mikew123/dic_ws/3dPrinted/Dicotomy-SwichProtectorClips.3mf

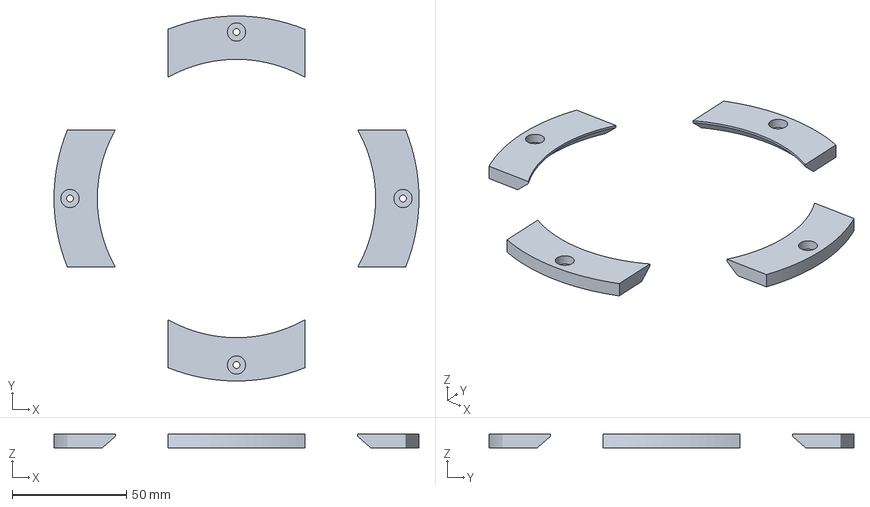
[picture p24: CAD file, 2026-02-28]
3dPrinted/Dicotomy-SwichProtectorClips.3mf
160.0 x 160.0 x 6.00 mm
