mikew123/dic_ws/3dPrinted/Dicotomy-clip.3mf

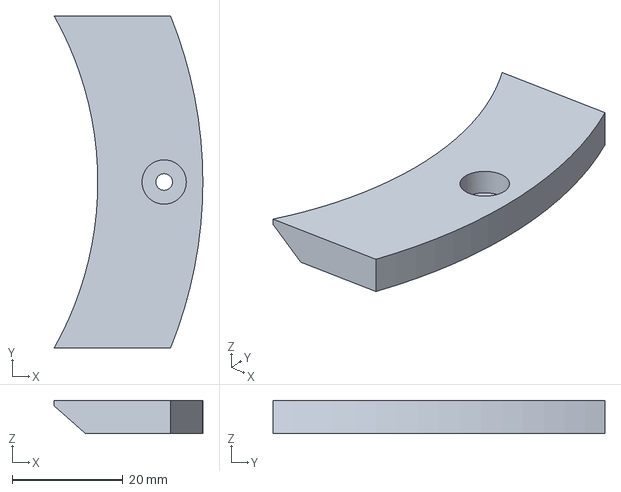
[picture p25: CAD file, 2026-02-28]
3dPrinted/Dicotomy-clip.3mf
26.9 x 60.0 x 6.00 mm
