mikew123/dic_ws/3dPrinted/Dicotomy-ElecMount.3mf

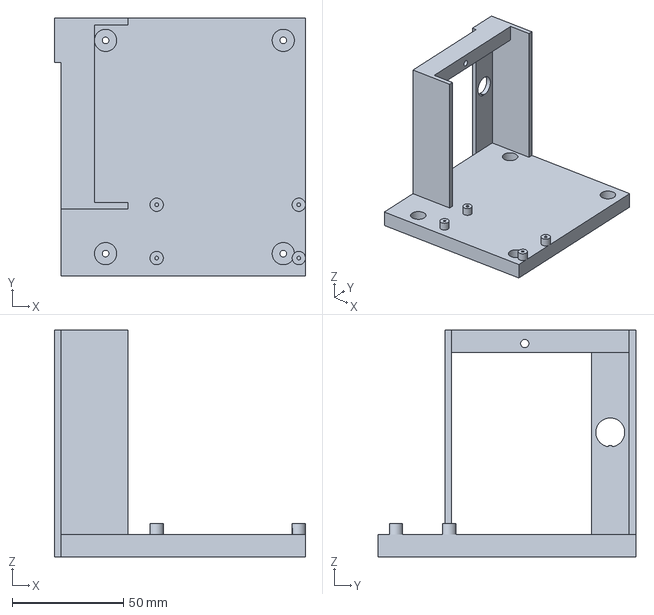
[picture p26: CAD file, 2026-02-23]
3dPrinted/Dicotomy-ElecMount.3mf
113.0 x 116.0 x 102.0 mm
