mikew123/dic_ws/3dPrinted/Dicotomy-CenteringRing.3mf

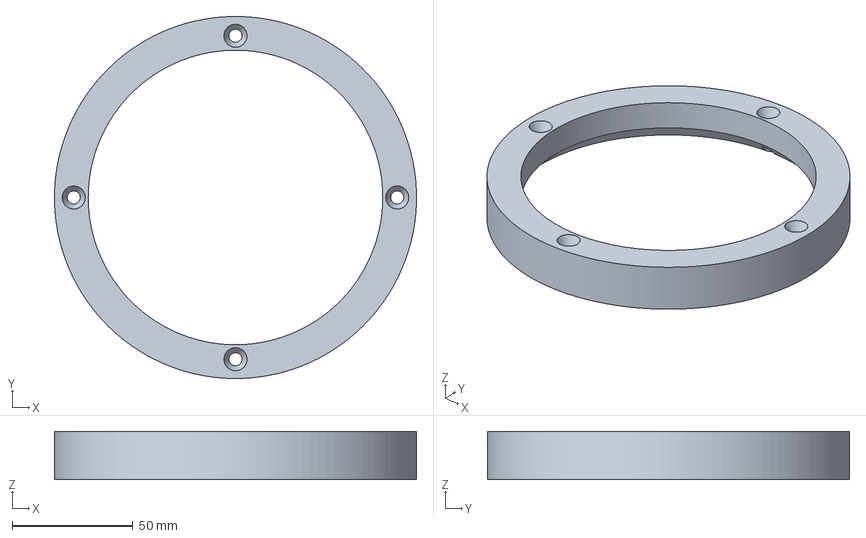
[picture p27: CAD file, 2026-02-21]
3dPrinted/Dicotomy-CenteringRing.3mf
150.0 x 150.0 x 20.0 mm
