mikew123/dic_ws/3dPrinted/Dicotomy-CenterHousing.3mf

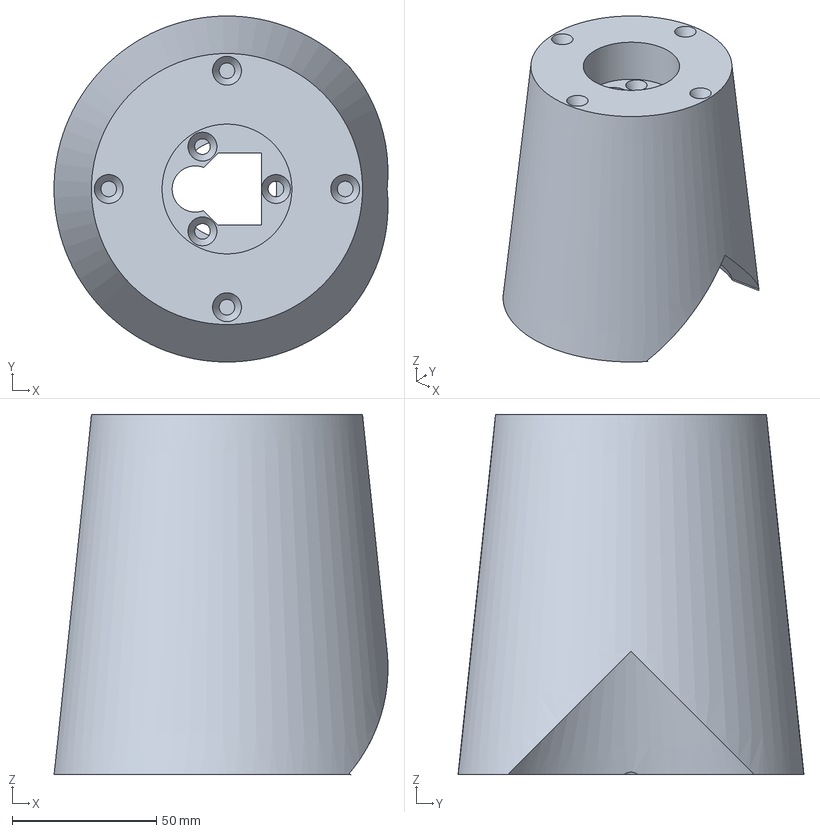
[picture p28: CAD file, 2026-02-21]
3dPrinted/Dicotomy-CenterHousing.3mf
115.8 x 120.0 x 125.0 mm
