mikew123/dic_ws/3dPrinted/Dicotomy-HumpCurved.3mf

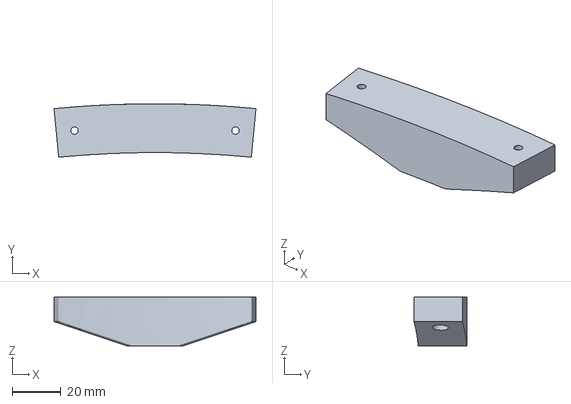
[picture p29: CAD file, 2026-02-21]
3dPrinted/Dicotomy-HumpCurved.3mf
82.8 x 21.9 x 20.0 mm
