mikew123/dic_ws/3dPrinted/Dicotomy-LimitSwHump.3mf

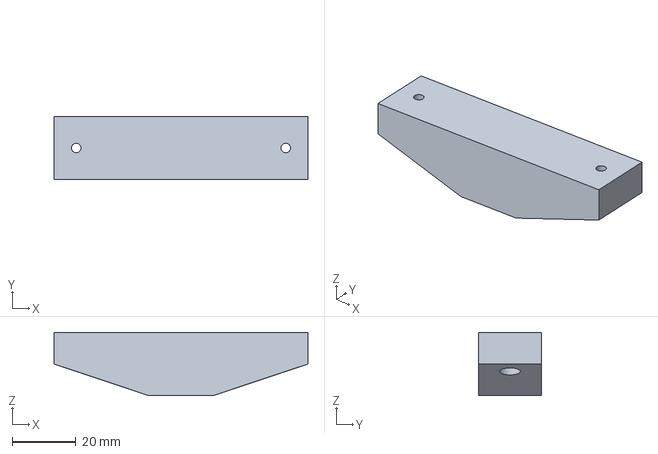
[picture p30: CAD file, 2026-02-21]
3dPrinted/Dicotomy-LimitSwHump.3mf
80.0 x 20.0 x 20.0 mm
