mikew123/dic_ws/3dPrinted/Dicotomy-LimtSwMount.3mf

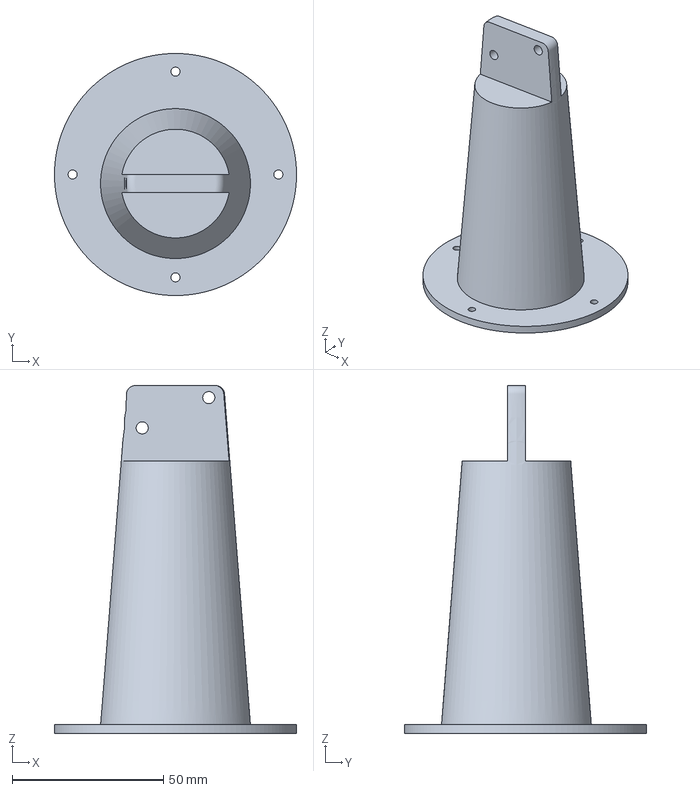
[picture p31: CAD file, 2026-02-21]
3dPrinted/Dicotomy-LimtSwMount.3mf
80.0 x 80.0 x 115.0 mm
